JanB97/RykerConnect/Software/PlatformIO/RykerConnect/src/functions.cpp

#include "functions.h"
#include <CRC32.h>
#include <Preferences.h>
#include <mcp9808.h>

bool h12Flag;
bool pmFlag;
void MCP_shutdown_wake(boolean sw);

void runTimers(){
  unsigned long currentMillis = millis();
  if(currentMillis - previousBatteryIconMillis >= sEEPROM.battery_icon_interval){
      previousBatteryIconMillis = currentMillis;
      int check_next = batteryIconSelection+1;
      if (check_next > sizeof(sEEPROM.battery_icon_selection)){
        check_next = 0;
      }
      for(int i = check_next; i<sizeof(sEEPROM.battery_icon_selection); i++){
          if(sEEPROM.battery_icon_selection[i]){
            batteryIconSelection = i;
            goto after_battery_selection;
          }
      }
      if(check_next != 0){
          for(int i = 0; i<check_next; i++){
            if(sEEPROM.battery_icon_selection[i]){
              batteryIconSelection = i;
              goto after_battery_selection;
            }
          }
      }
      batteryIconSelection = -1;

  }
  after_battery_selection:
  if(playstate){
    if (currentMillis - previousMusicMillis >= musicInterval) { //Music Zeit / Bar
      previousMusicMillis = currentMillis;
      music_timer++;
    }}else{
      previousMusicMillis = currentMillis;}
  
  if (currentMillis - previousScrollTitleMillis >= scrollTitleInterval) { // Title Scrolling
    previousScrollTitleMillis = currentMillis;
    if(scroll_title_en){
        scroll_title++;
    }
  }
  if (currentMillis - previousScrollArtistMillis >= scrollArtistInterval) { // Artist Scrolling
    previousScrollArtistMillis = currentMillis;
    if(scroll_artist_en){
        scroll_artist++;
    }
  }
  if(previousNotificationMillis != 0){
    if(currentMillis - previousNotificationMillis >= sEEPROM.notification_interval){
      notificationDisplayed = false;
    }
  }
  if(previousResetMillis != 0){
    if(currentMillis - previousResetMillis >= RESET_INTERVAL){
        previousResetMillis = 0;
    }
  }

  // Time and Temp
  if(currentMillis - previousTimeMillis >= TIME_INTERVAL){
      previousTimeMillis = currentMillis;
      global_time = timeString(RTC.getHour(h12Flag, pmFlag)) + ":" + timeString(RTC.getMinute());
  }
  if(currentMillis - previousTempMillis >= TEMP_INTERVAL){
      previousTempMillis = currentMillis;
      if(ts.isConnected()){
        //MCP_shutdown_wake(false);
        //delay(65);
        global_temp = ts.getTemperature() - sEEPROM.temp_calibration;
        //MCP_shutdown_wake(true);
      }else{
        global_temp = RTC.getTemperature() - sEEPROM.temp_calibration;
      }     
  }

  // Volume popup auto-dismiss
  if(volumeDisplayed && currentMillis - previousVolumeMillis >= (unsigned long)VOLUME_POPUP_DURATION_DEFAULT * 1000UL){
      volumeDisplayed = false;
  }

  // Popup auto-dismiss (configurable duration for all warning popups)
  unsigned long popupDurationMs = (unsigned long)sEEPROM.warning_popup_duration * 1000UL;
  if(popupDurationMs == 0) popupDurationMs = 1000;

  // Low battery popup auto-dismiss
  if(lowBatteryDisplayed && currentMillis - previousLowBatteryMillis >= popupDurationMs){
      lowBatteryDisplayed = false;
  }

  // Auto-Brightness (EMA smoothing)
  if(sEEPROM.adaptive_brightness && currentMillis - previousAutoBrightnessMillis >= AUTO_BRIGHTNESS_INTERVAL){
      previousAutoBrightnessMillis = currentMillis;
      int raw = analogRead(lightSensorPin);
      if(smoothedLightLevel < 0){
          smoothedLightLevel = raw;
      } else {
          smoothedLightLevel = smoothedLightLevel * 0.95f + raw * 0.05f;
      }
      uint16_t adcLow  = sEEPROM.auto_brightness_adc_low;
      uint16_t adcHigh = sEEPROM.auto_brightness_adc_high;
      if(adcHigh <= adcLow){ adcLow = AUTO_BRIGHTNESS_ADC_LOW_DEFAULT; adcHigh = AUTO_BRIGHTNESS_ADC_HIGH_DEFAULT; }
      uint8_t brightness = map(constrain((int)smoothedLightLevel, adcLow, adcHigh), adcLow, adcHigh, AUTO_BRIGHTNESS_MIN, AUTO_BRIGHTNESS_MAX);
      u8g2_0.setContrast(brightness);
      u8g2_1.setContrast(brightness);
  }

  // BLE stale connection watchdog
  if(blConnected && lastBLEActivityMillis > 0 && currentMillis - lastBLEActivityMillis >= BLE_STALE_TIMEOUT){
      D_println("BLE: Stale connection detected, disconnecting...");
      blConnected = false;
      lastBLEActivityMillis = 0;
      NimBLEServer* pServer = NimBLEDevice::getServer();
      if(pServer && pServer->getConnectedCount() > 0){
          pServer->disconnect(pServer->getPeerInfo(0).getConnHandle());
      }
  }
}


void MCP_shutdown_wake(boolean sw) {
  uint16_t conf_shutdown;
  uint16_t conf_register = ts.getConfigRegister();
  if (sw == true) {
    conf_shutdown = conf_register | MCP9808_SHUTDOWN;
  }
  else {
    conf_shutdown = conf_register & ~MCP9808_SHUTDOWN;
  }
  ts.setConfigRegister(conf_shutdown);
}


String timeString(uint8_t value){
  if(value<10){
    return "0" + String(value);
  }
  return String(value);
}

void reset_settings(){
    sEEPROM.adaptive_brightness = ADAPTIVE_BRIGHTNESS;
    sEEPROM.display_brightness = DISPLAY_BRIGHTNESS;
    sEEPROM.screen = SCREEN_SELECTION;
    sEEPROM.sub_screen = SUB_SCREEN_SELECTION;
    sEEPROM.battery_icon_selection[0] = BATTERY_ICON_SELECTION1;
    sEEPROM.battery_icon_selection[1] = BATTERY_ICON_SELECTION2;
    sEEPROM.battery_icon_selection[2] = BATTERY_ICON_SELECTION3;
    sEEPROM.battery_icon_selection[3] = BATTERY_ICON_SELECTION4;
    sEEPROM.battery_icon_first = BATTERY_ICON_FIRST;
    sEEPROM.battery_icon_interval = BATTERY_ICON_INTERVAL;
    sEEPROM.notification_interval = NOTIFICATION_INTERVAL;
    sEEPROM.temp_calibration = 0.0;
    sEEPROM.low_battery_threshold_phone = LOW_BATTERY_THRESHOLD_PHONE_DEFAULT;
    sEEPROM.low_battery_threshold_intercom = LOW_BATTERY_THRESHOLD_INTERCOM_DEFAULT;
    sEEPROM.warning_popup_duration = WARNING_POPUP_DURATION_DEFAULT;
    sEEPROM.auto_brightness_adc_low = AUTO_BRIGHTNESS_ADC_LOW_DEFAULT;
    sEEPROM.auto_brightness_adc_high = AUTO_BRIGHTNESS_ADC_HIGH_DEFAULT;
    memset(sEEPROM.reserved, 0, sizeof(sEEPROM.reserved));
    sEEPROM.crc = calc_crc();

    D_printf("Settings reset... \n New CRC: %i, Saving Settings to EEPROM", sEEPROM.crc);
    prefs.putBytes("settings", &sEEPROM, sizeof(EEPROM_Struct));
}

bool valiade_eeprom(){
  uint32_t crc = calc_crc();
  if(crc == sEEPROM.crc){
    D_println("CRC MATCH!");
    return true;
  }
  D_println("CRC DOES NOT MATCH!");
  return false;
}

uint32_t calc_crc(){
  //uint8_t numBuff = sizeof(EEPROM_Struct)-sizeof(sEEPROM.crc)-3;
  static constexpr uint8_t numBuff = sizeof(EEPROM_Struct)-sizeof(uint32_t);
  uint8_t crcBuffer[numBuff];
  memcpy(crcBuffer, &sEEPROM,numBuff);
  uint32_t crc = CRC32::calculate(crcBuffer, sizeof(crcBuffer));
  D_println();
  D_printf("Size Of CRC: %i", sizeof(sEEPROM.crc));
  D_printf("Size of Struct: %i", sizeof(EEPROM_Struct));
  #ifdef DEBUG
  D_print("| ");
  for (int i = 0; i<numBuff;i++){
    D_print(crcBuffer[i], BIN);
    D_print(" | ");
  }
  #endif
  D_println("");
  D_print("CRC alt: ");
  D_println(sEEPROM.crc, HEX);   
  D_print("CRC neu: ");
  D_println(crc, HEX);
  
  return crc;
}
