JanB97/RykerConnect/Software/PlatformIO/RykerConnect/include/main.h

#pragma once

#include <Arduino.h>
#include <U8g2lib.h>
#include <SPI.h>
#include "functions.h"
#include "func_gui.h"
#include "func_u8g2.h"
#include "global_vars.h"

#include <NimBLEDevice.h>
#include <NimBLEHIDDevice.h>
#include "HIDTypes.h"
#include "ble_server.h"
